kounocom/CosmicLSM/Outputs/board.png

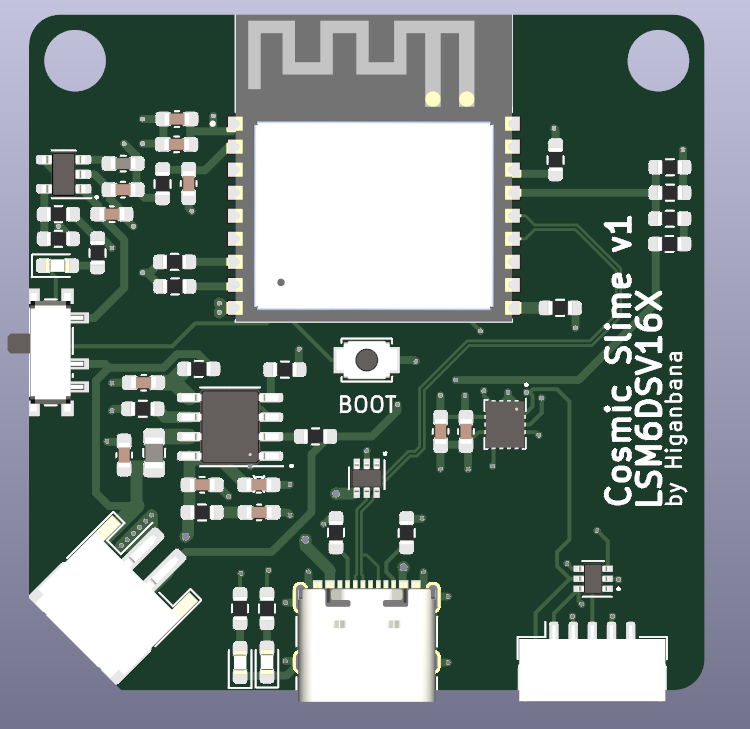
Outputs/board.png
