kounocom/CosmicLSM/Outputs/schematic.png

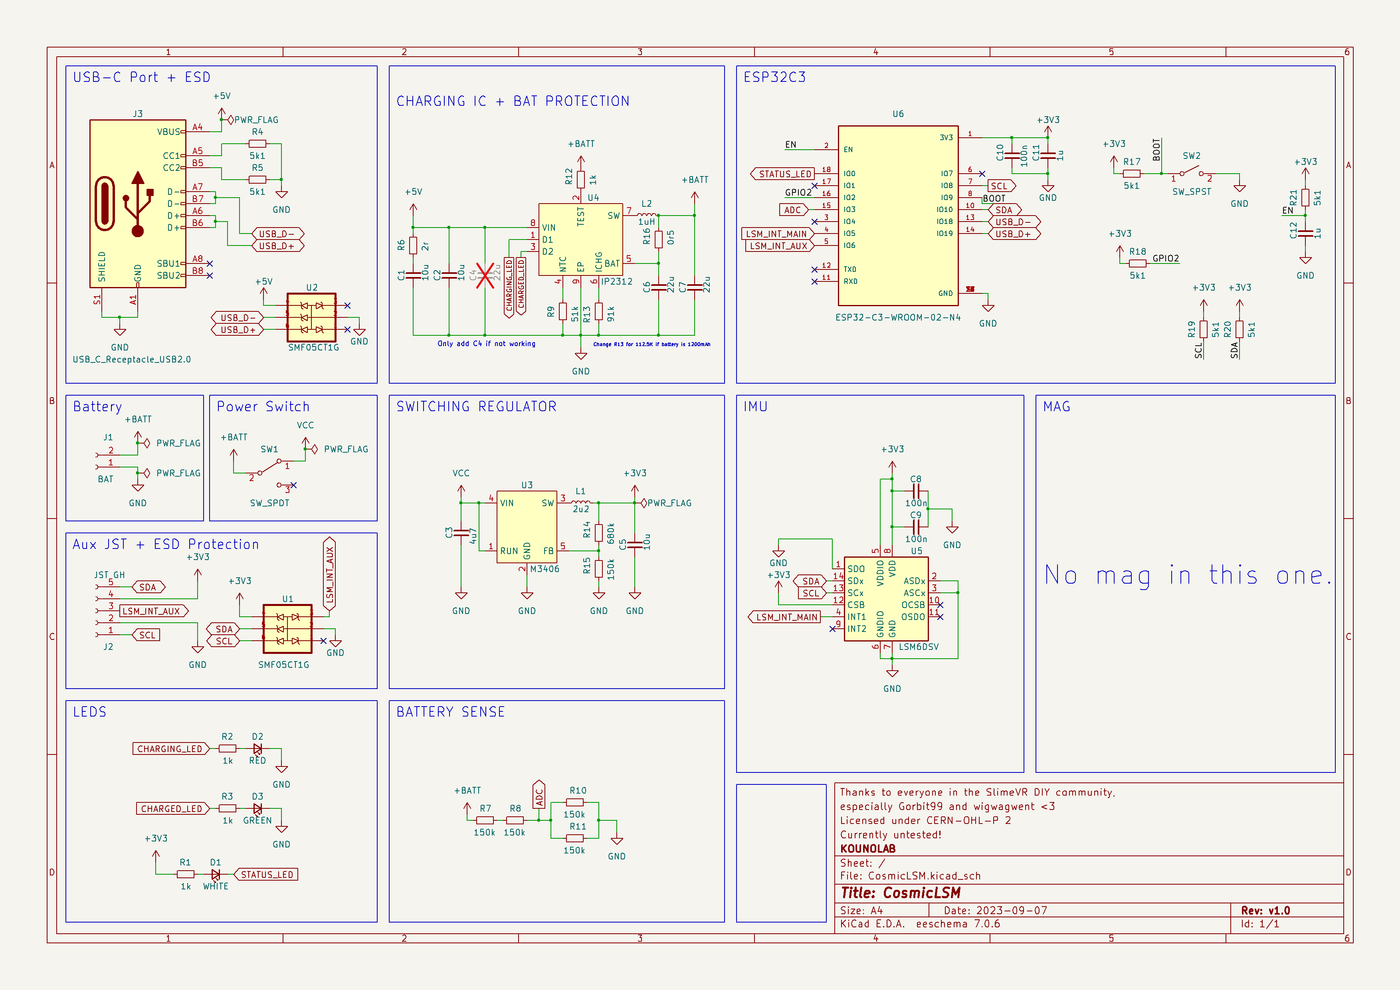
Outputs/schematic.png
